yaz-gear/iot-agricultural-pole-sensor/hardware/CAD_models/png/Screenshot 2023-04-07 222702.png

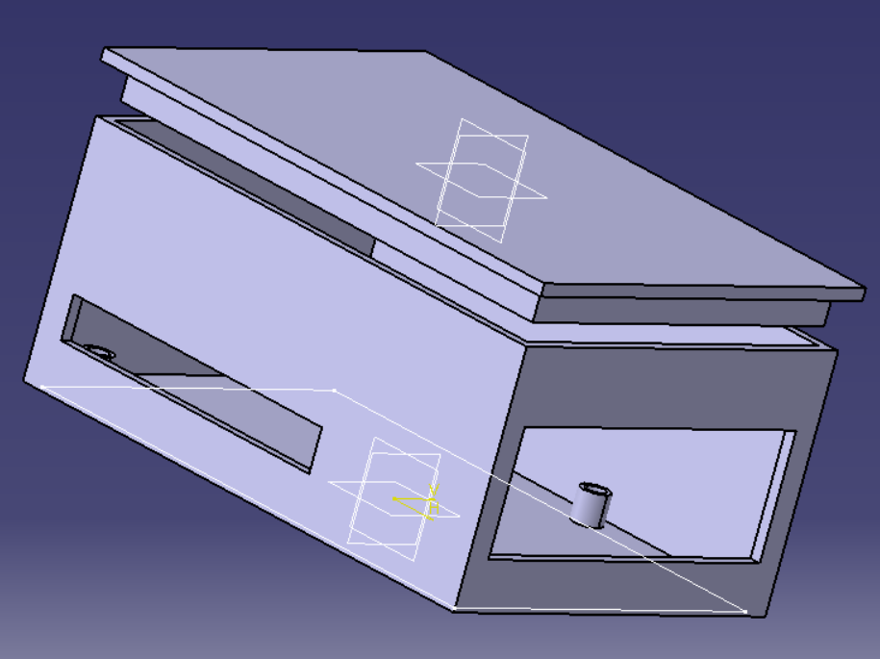
hardware/CAD_models/png/Screenshot 2023-04-07 222702.png
