yaz-gear/iot-agricultural-pole-sensor/src/esp32/mqtt_client.cpp

#include <WiFi.h>
#include <PubSubClient.h>

const char* ssid = "YOUR_SSID";
const char* password = "YOUR_PASSWORD";
const char* mqtt_server = "RASPBERRY_PI_IP";

WiFiClient espClient;
PubSubClient client(espClient);

void setup_wifi() {
  WiFi.begin(ssid, password);
  while (WiFi.status() != WL_CONNECTED) {
    delay(500);
    Serial.print(".");
  }
  Serial.println("WiFi connected");
}

void reconnect() {
  while (!client.connected()) {
    if (client.connect("ESP32Client")) {
      Serial.println("Connected to MQTT broker");
    } else {
      delay(5000);
    }
  }
}
